concept-code-design/push-n-turn-midi61/software/push-n-turn61/colors.h

#define GREEN  10
#define GREENYELLOW     26
#define YELLOW          42
#define ORANGE          58
#define CRIMSON         74
#define RED             90
#define REDVIOLET       106
#define VIOLET          122
#define PURPLE          138
#define DEEPPURPLE      154
#define BLUE            170
#define AQUABLUE        186
#define AQUA            202
#define TURQOISE       218
#define TGREEN          234
#define GREEN2          250

#define CCLICK      TGREEN
#define CTOGGLE     AQUABLUE
#define CMOMENTARY YELLOW
#define CPROGMODE   RED
#define CKEYSELECT  PURPLE
#define CKEYACK     DEEPPURPLE
#define CPROGBOOT   CRIMSON


/* 256 color table (Wheel function)
https://raw.githubusercontent.com/wryan67/neopixel_rpi_lib/master/readme/ColorWheel.png

*/
